spartanracingelectric/SR-BMS/examples/stm32f105_blink/Core/Inc/main.h

#define MCU_USB_INT_Pin GPIO_PIN_0
#define MCU_USB_INT_GPIO_Port GPIOA
#define MCU_HEARTBEAT_LED_Pin GPIO_PIN_6
#define MCU_HEARTBEAT_LED_GPIO_Port GPIOC
#define PMUX_ST_Pin GPIO_PIN_8
#define PMUX_ST_GPIO_Port GPIOC
