spartanracingelectric/SR-BMS/examples/stm32f105_can/Core/Src/can.c

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
/* Includes ------------------------------------------------------------------*/
#include "can.h"

CAN_HandleTypeDef hcan1;
CAN_HandleTypeDef hcan2;

/* CAN1 init function */
void MX_CAN1_Init(void)
{

  hcan1.Instance = CAN1;
  hcan1.Init.Prescaler = 4;
  hcan1.Init.Mode = CAN_MODE_NORMAL;
  hcan1.Init.SyncJumpWidth = CAN_SJW_1TQ;
  hcan1.Init.TimeSeg1 = CAN_BS1_13TQ;
  hcan1.Init.TimeSeg2 = CAN_BS2_4TQ;
  hcan1.Init.TimeTriggeredMode = DISABLE;
  hcan1.Init.AutoBusOff = ENABLE;
  hcan1.Init.AutoWakeUp = DISABLE;
  hcan1.Init.AutoRetransmission = ENABLE;
  hcan1.Init.ReceiveFifoLocked = DISABLE;
  hcan1.Init.TransmitFifoPriority = DISABLE;
  if (HAL_CAN_Init(&hcan1) != HAL_OK)
  {
    Error_Handler();
  }
}
/* CAN2 init function */
void MX_CAN2_Init(void)
{

  hcan2.Instance = CAN2;
  hcan2.Init.Prescaler = 4;
  hcan2.Init.Mode = CAN_MODE_NORMAL;
  hcan2.Init.SyncJumpWidth = CAN_SJW_1TQ;
  hcan2.Init.TimeSeg1 = CAN_BS1_13TQ;
  hcan2.Init.TimeSeg2 = CAN_BS2_4TQ;
  hcan2.Init.TimeTriggeredMode = DISABLE;
  hcan2.Init.AutoBusOff = ENABLE;
  hcan2.Init.AutoWakeUp = DISABLE;
  hcan2.Init.AutoRetransmission = ENABLE;
  hcan2.Init.ReceiveFifoLocked = DISABLE;
  hcan2.Init.TransmitFifoPriority = DISABLE;
  if (HAL_CAN_Init(&hcan2) != HAL_OK)
  {
    Error_Handler();
  }
}

static uint32_t HAL_RCC_CAN1_CLK_ENABLED=0;

void HAL_CAN_MspInit(CAN_HandleTypeDef* canHandle)
{

  GPIO_InitTypeDef GPIO_InitStruct = {0};
  if(canHandle->Instance==CAN1)
  {
    /* CAN1 clock enable */
    HAL_RCC_CAN1_CLK_ENABLED++;
    if(HAL_RCC_CAN1_CLK_ENABLED==1){
      __HAL_RCC_CAN1_CLK_ENABLE();
    }

    __HAL_RCC_GPIOB_CLK_ENABLE();
    /**CAN1 GPIO Configuration
    PB8     ------> CAN1_RX
    PB9     ------> CAN1_TX
    */
    GPIO_InitStruct.Pin = GPIO_PIN_8;
    GPIO_InitStruct.Mode = GPIO_MODE_INPUT;
    GPIO_InitStruct.Pull = GPIO_NOPULL;
    HAL_GPIO_Init(GPIOB, &GPIO_InitStruct);

    GPIO_InitStruct.Pin = GPIO_PIN_9;
    GPIO_InitStruct.Mode = GPIO_MODE_AF_PP;
    GPIO_InitStruct.Speed = GPIO_SPEED_FREQ_HIGH;
    HAL_GPIO_Init(GPIOB, &GPIO_InitStruct);

    __HAL_AFIO_REMAP_CAN1_2();

  }
  else if(canHandle->Instance==CAN2)
  {
    /* CAN2 clock enable */
    __HAL_RCC_CAN2_CLK_ENABLE();
    HAL_RCC_CAN1_CLK_ENABLED++;
    if(HAL_RCC_CAN1_CLK_ENABLED==1){
      __HAL_RCC_CAN1_CLK_ENABLE();
    }

    __HAL_RCC_GPIOB_CLK_ENABLE();
    /**CAN2 GPIO Configuration
    PB12     ------> CAN2_RX
    PB13     ------> CAN2_TX
    */
    GPIO_InitStruct.Pin = GPIO_PIN_12;
    GPIO_InitStruct.Mode = GPIO_MODE_INPUT;
    GPIO_InitStruct.Pull = GPIO_NOPULL;
    HAL_GPIO_Init(GPIOB, &GPIO_InitStruct);

    GPIO_InitStruct.Pin = GPIO_PIN_13;
    GPIO_InitStruct.Mode = GPIO_MODE_AF_PP;
    GPIO_InitStruct.Speed = GPIO_SPEED_FREQ_HIGH;
    HAL_GPIO_Init(GPIOB, &GPIO_InitStruct);

  }
}

void HAL_CAN_MspDeInit(CAN_HandleTypeDef* canHandle)
{

  if(canHandle->Instance==CAN1)
  {
    /* Peripheral clock disable */
    HAL_RCC_CAN1_CLK_ENABLED--;
    if(HAL_RCC_CAN1_CLK_ENABLED==0){
      __HAL_RCC_CAN1_CLK_DISABLE();
    }

    /**CAN1 GPIO Configuration
    PB8     ------> CAN1_RX
    PB9     ------> CAN1_TX
    */
    HAL_GPIO_DeInit(GPIOB, GPIO_PIN_8|GPIO_PIN_9);

  }
  else if(canHandle->Instance==CAN2)
  {
    /* Peripheral clock disable */
    __HAL_RCC_CAN2_CLK_DISABLE();
    HAL_RCC_CAN1_CLK_ENABLED--;
    if(HAL_RCC_CAN1_CLK_ENABLED==0){
      __HAL_RCC_CAN1_CLK_DISABLE();
    }

    /**CAN2 GPIO Configuration
    PB12     ------> CAN2_RX
    PB13     ------> CAN2_TX
    */
    HAL_GPIO_DeInit(GPIOB, GPIO_PIN_12|GPIO_PIN_13);

  }
}

/* USER CODE BEGIN 1 */
HAL_StatusTypeDef CAN1_Start() {
	return HAL_CAN_Start(&hcan1);
}

HAL_StatusTypeDef CAN1_Tx(const CAN_TxHeaderTypeDef *pHeader, const uint8_t aData[], uint32_t *pTxMailbox) {
	return HAL_CAN_AddTxMessage(&hcan1, pHeader, aData, pTxMailbox);
}

uint32_t CAN1_CheckError() {
	return hcan1.ErrorCode;
}

uint32_t CAN1_GetTxMailboxesFreeLevel() {
	return HAL_CAN_GetTxMailboxesFreeLevel(&hcan1);
}
/* USER CODE END 1 */
